upenn-embedded/final-project-s26-t1/sprint2-media/drawing program.jpg

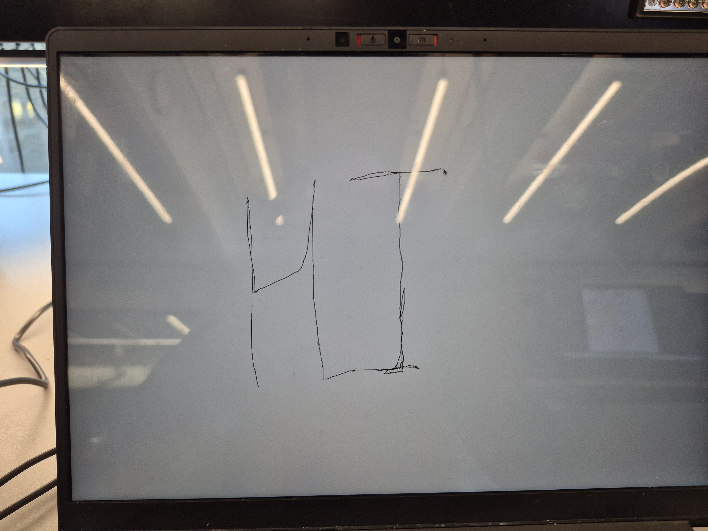
sprint2-media/drawing program.jpg
