upenn-embedded/final-project-s26-t1/sprint2-media/Enclosure1.jpg

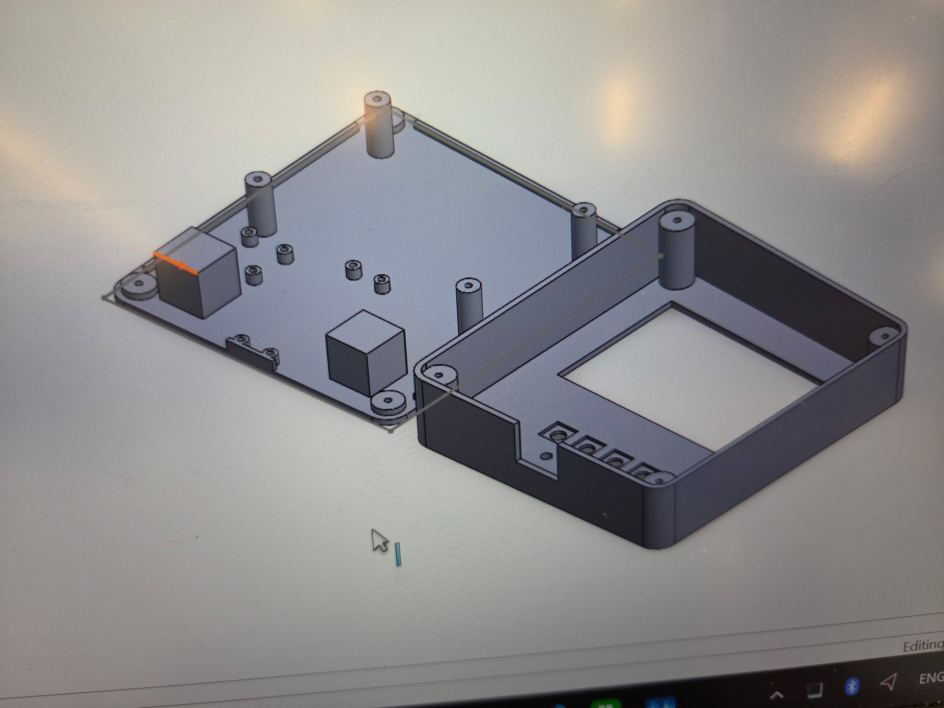
sprint2-media/Enclosure1.jpg
