upenn-embedded/final-project-s26-t1/sprint2-media/Enclosure3.jpg

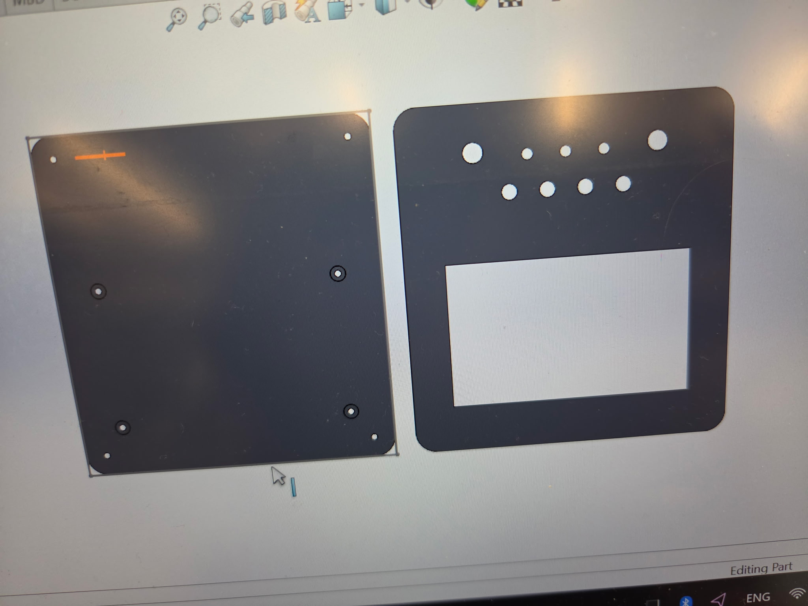
sprint2-media/Enclosure3.jpg
