upenn-embedded/final-project-s26-t1/website-media/400x400-digital-etch-a-sketch.jpg

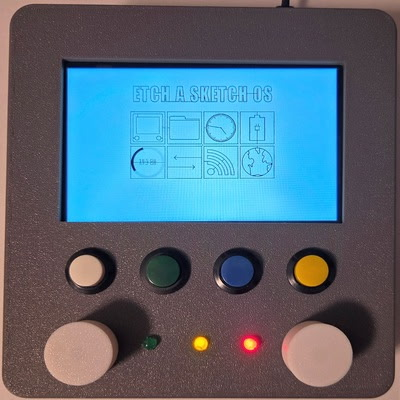
website-media/400x400-digital-etch-a-sketch.jpg
