upenn-embedded/final-project-s26-t1/website-media/cameron-shaw.jpg

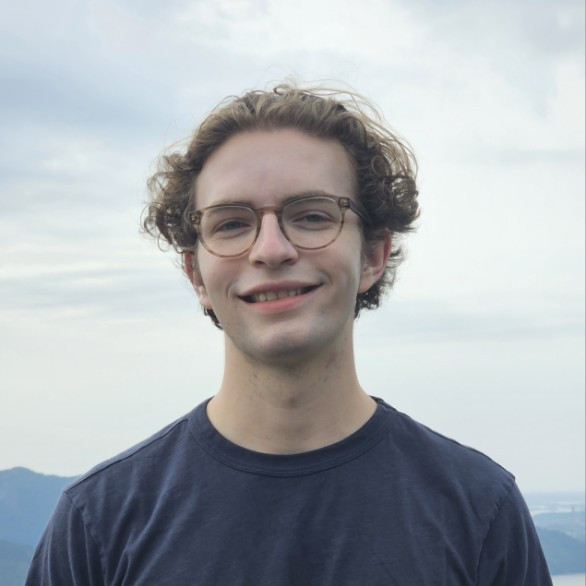
website-media/cameron-shaw.jpg
