upenn-embedded/final-project-s26-t1/website-media/clayton-hickey.webp

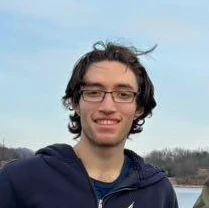
website-media/clayton-hickey.webp
