upenn-embedded/final-project-s26-t1/website-media/elan-goldman.png

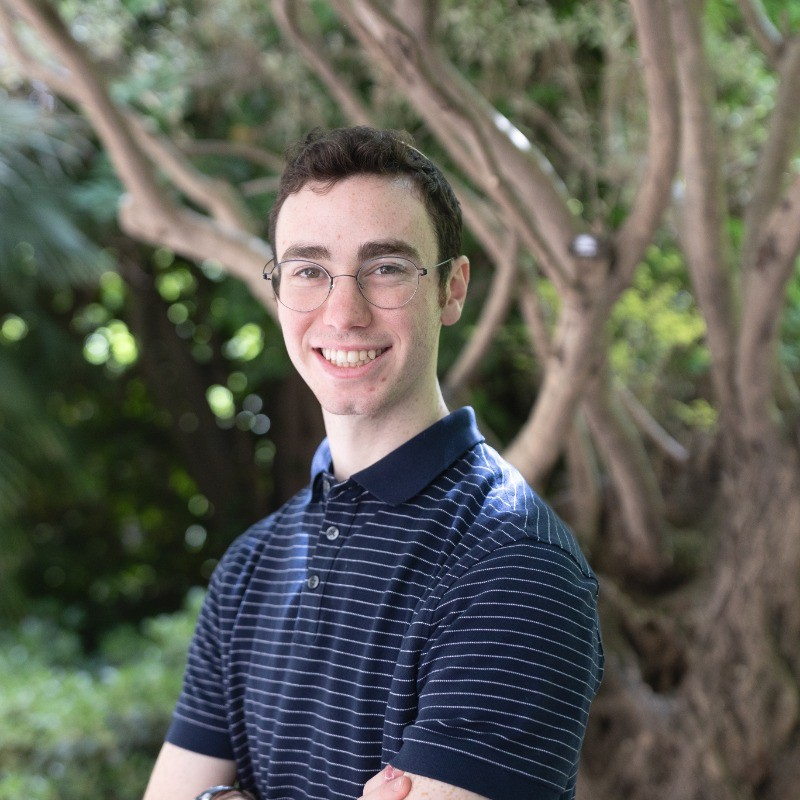
website-media/elan-goldman.png
