upenn-embedded/final-project-s26-t1/website-media/front-booting.jpeg

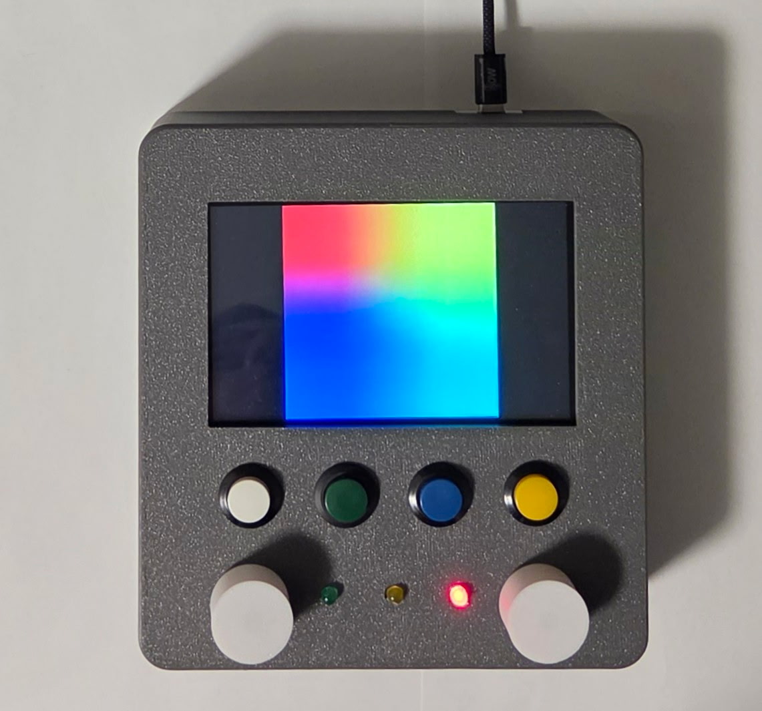
website-media/front-booting.jpeg
