upenn-embedded/final-project-s26-t1/website-media/front-drawing.jpeg

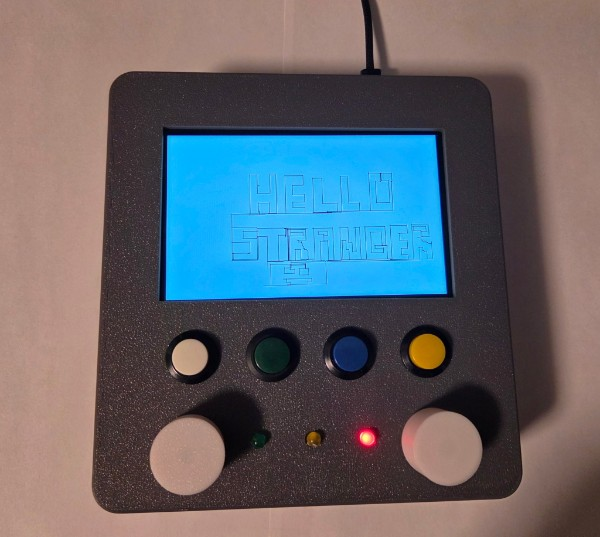
website-media/front-drawing.jpeg
