upenn-embedded/final-project-s26-t1/website-media/internals-input.jpeg

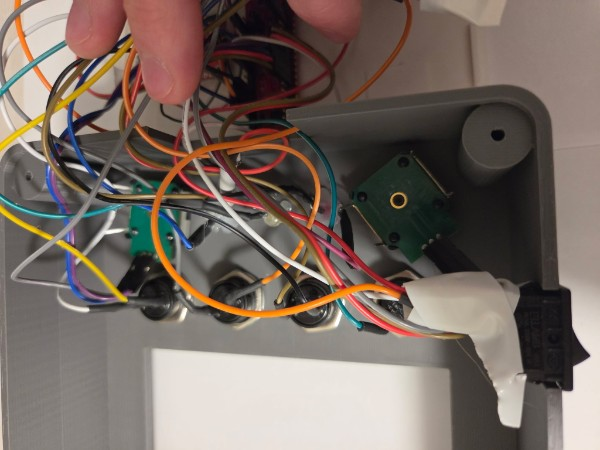
website-media/internals-input.jpeg
