upenn-embedded/final-project-s26-t1/website-media/internals-unfolded-far.jpeg

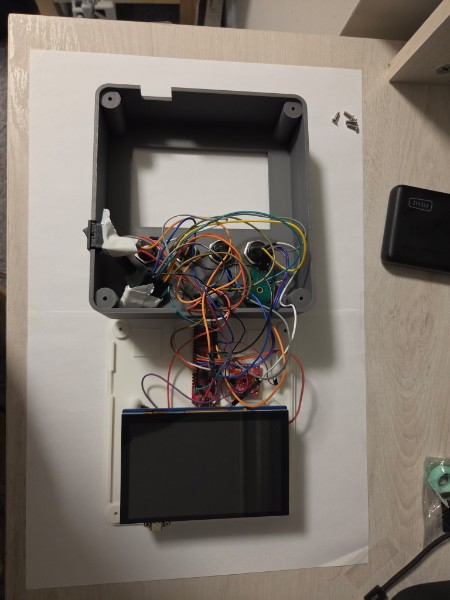
website-media/internals-unfolded-far.jpeg
