upenn-embedded/final-project-s26-t1/website-media/internals-unfolded.jpeg

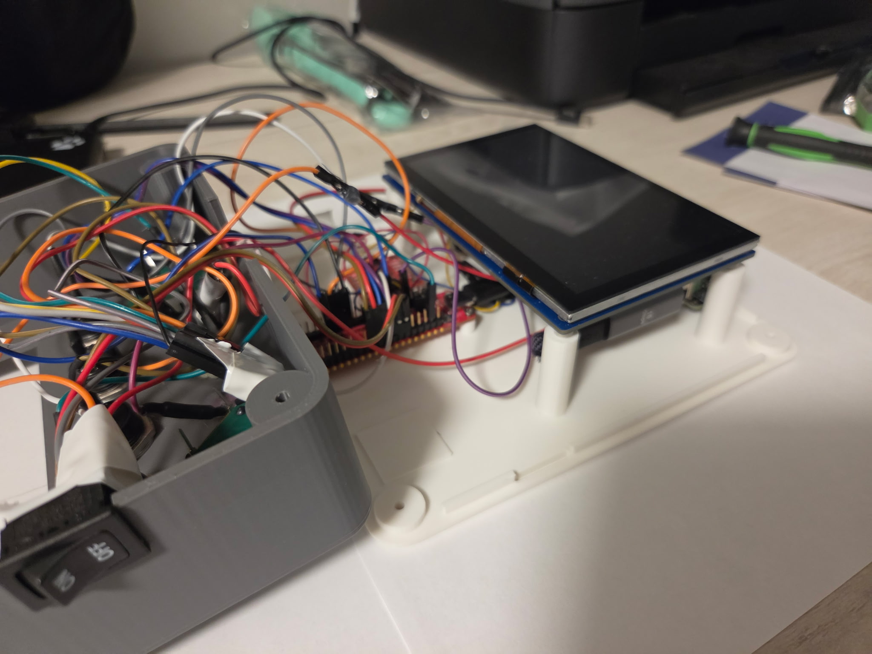
website-media/internals-unfolded.jpeg
