upenn-embedded/final-project-s26-t1/website-media/top-back.jpeg

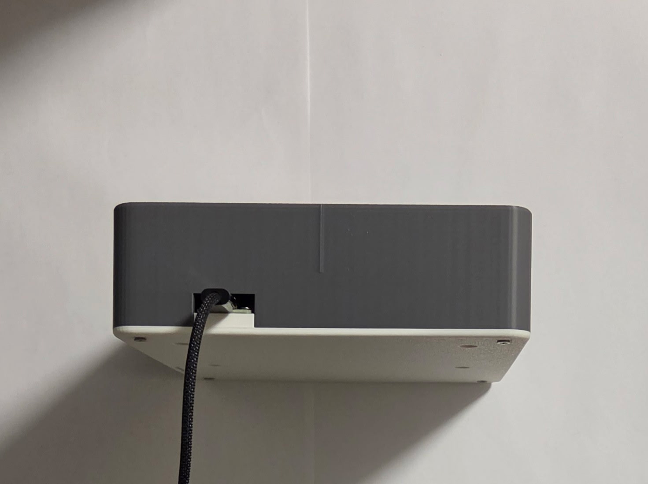
website-media/top-back.jpeg
