upenn-embedded/final-project-s26-t1/website-media/top-drawing.jpeg

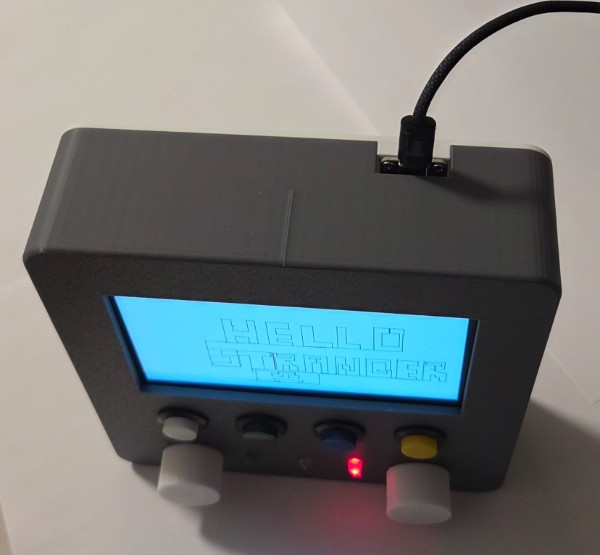
website-media/top-drawing.jpeg
