upenn-embedded/final-project-s26-t1/sprint2-media/wrapped dashboard config on pi.jpg

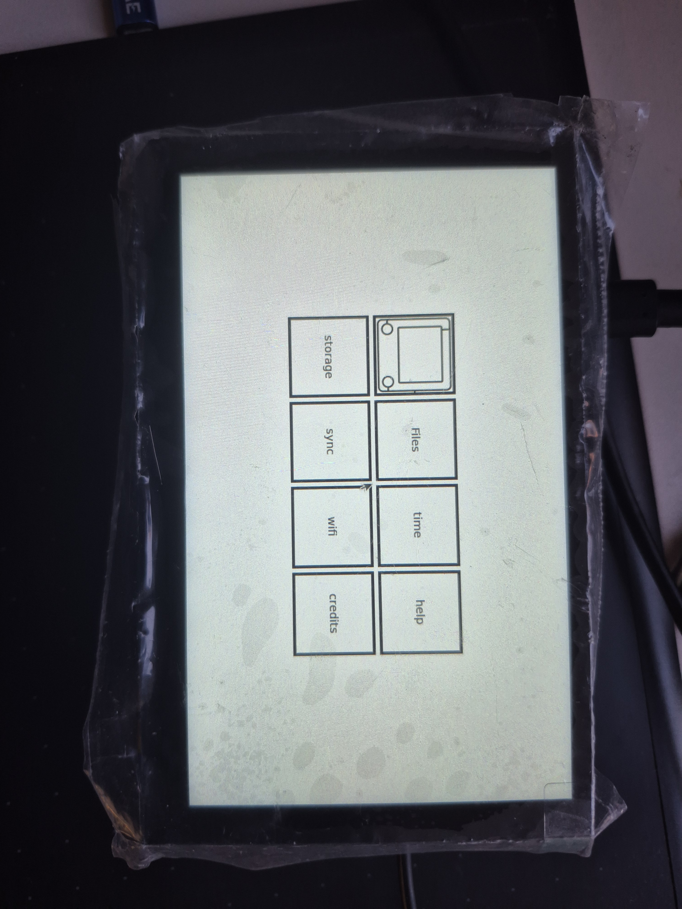
sprint2-media/wrapped dashboard config on pi.jpg
